thekakkun/Callisto/firmware/src/display.h

#ifndef DISPLAY_H
#define DISPLAY_H

#include <Arduino.h>
#include <SPI.h>
#include <movingAvg.h>
#include <esp_sleep.h>

extern const int LDR_PIN;
extern movingAvg ldr_reading;
extern const int BOOST_CHANNEL;
extern const int BLANK_CHANNEL;
void adjust_brightness(int min_brightness, int max_brightness);
void utilities(int *min_brightness, int *max_brightness);
extern const int TOUCH_THRESHOLD;
void set_touch_state(bool &touch_state, bool &previous_touch_state,
                     unsigned long &touch_start, unsigned long &touch_end);

extern bool ap_active;
extern bool wifi_connected;
extern bool credentials_saved;
extern bool server_active;
extern bool time_synced;
extern const int VFBLANK;
extern unsigned long touch_wake_time;

enum Mode
{
    current_time,
    in_sleep,
    current_date,
    ip_address,
    ntp_syncing,
    wifi_error,
    connect_ap
};

bool is_night(bool touch_state);
void go_to_sleep();
Mode get_mode();
void set_text(Mode disp_mode, char *disp_text);

void dot_scroll(int *dots);
void set_dots(Mode disp_mode, int *dots);

extern int dot;
extern int font_table[46];
extern int digit_table[9];
extern const int VFLOAD;
int get_spi_data(int current_digit, char *disp_text, int *dots);
void send_spi_data(int spi_data);

extern unsigned long last_brightness_damper;
extern unsigned long last_wifi_check;

#endif
